lukbieli/DC_meter/case_model/DC_Meter_Case - Surface 7.stl

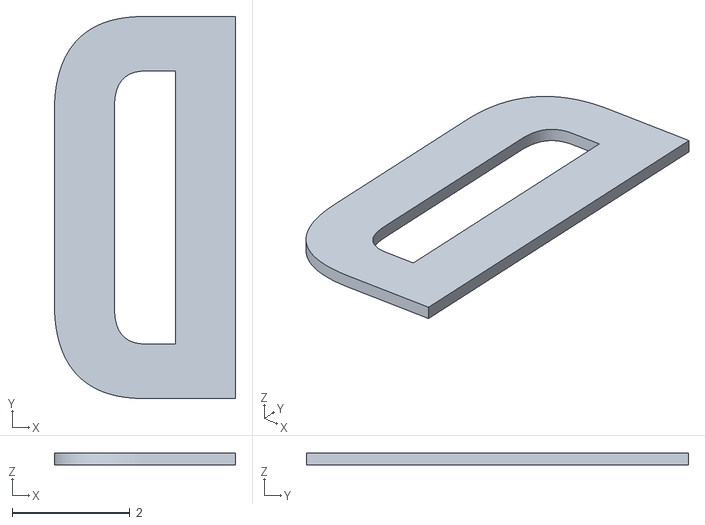
[picture p23: CAD file, 2025-07-14]
case_model/DC_Meter_Case - Surface 7.stl
3.08 x 6.49 x 0.2
