lukbieli/DC_meter/case_model/DC_Meter_Case - Surface 29.stl

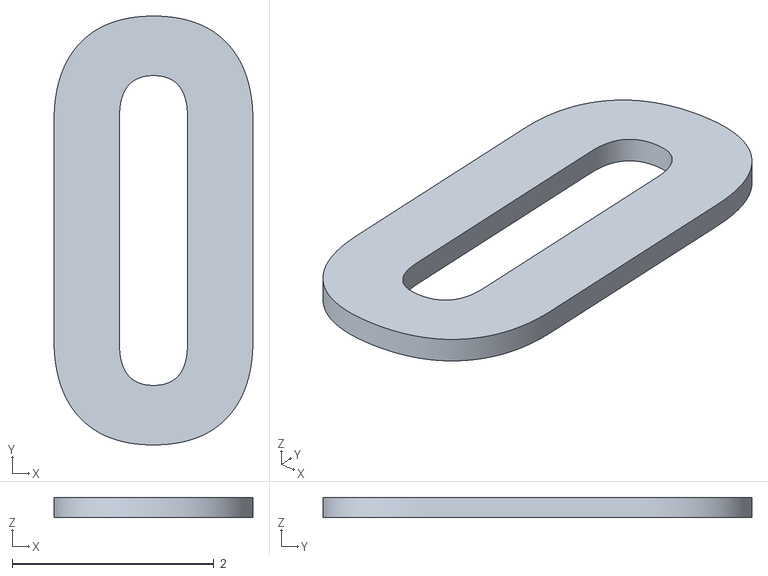
[picture p24: CAD file, 2025-07-14]
case_model/DC_Meter_Case - Surface 29.stl
1.97 x 4.26 x 0.2
