lukbieli/DC_meter/case_model/DC_Meter_Case - Surface 23.stl

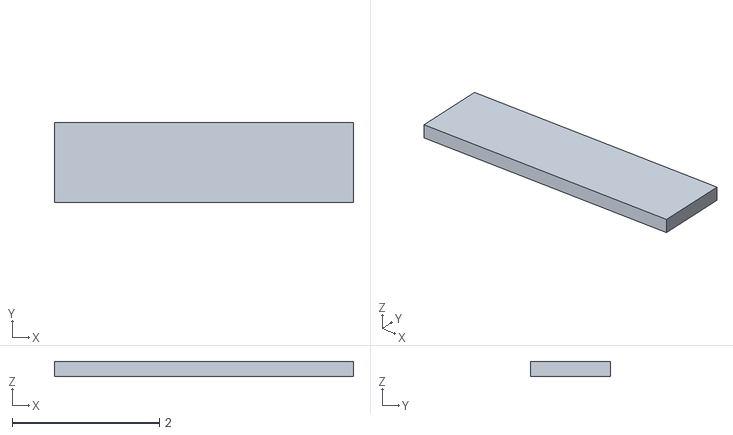
[picture p25: CAD file, 2025-07-14]
case_model/DC_Meter_Case - Surface 23.stl
4.06 x 1.08 x 0.2
