lukbieli/DC_meter/case_model/DC_Meter_Case - Surface 52.stl

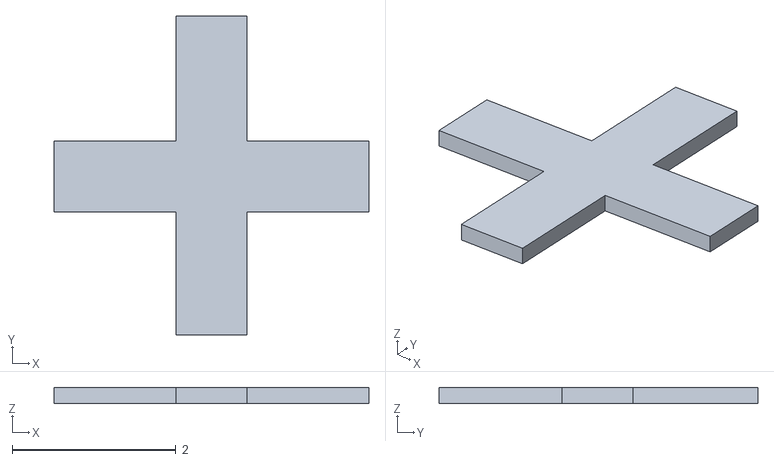
[picture p26: CAD file, 2025-07-14]
case_model/DC_Meter_Case - Surface 52.stl
3.84 x 3.89 x 0.2
