lukbieli/DC_meter/case_model/DC_Meter_Case - Surface 47.stl

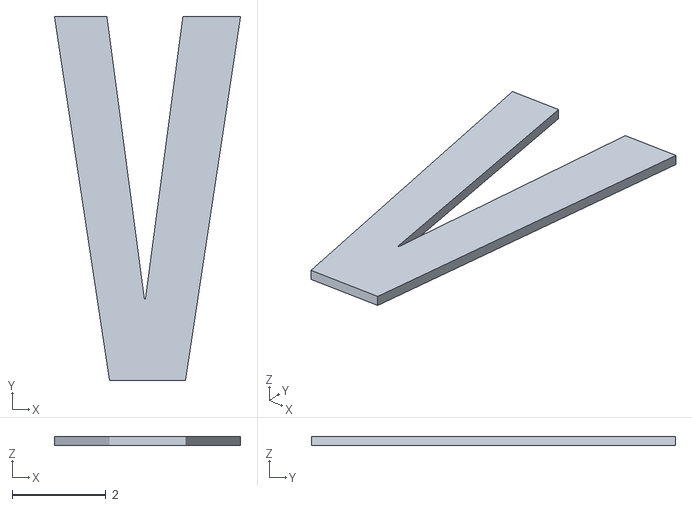
[picture p27: CAD file, 2025-07-14]
case_model/DC_Meter_Case - Surface 47.stl
3.98 x 7.78 x 0.2
