lukbieli/DC_meter/case_model/DC_Meter_Case - Surface 34.stl

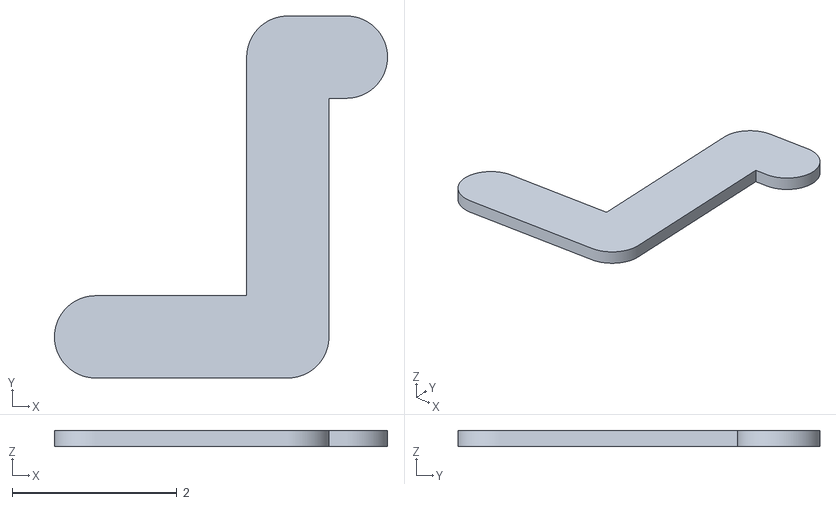
[picture p28: CAD file, 2025-07-14]
case_model/DC_Meter_Case - Surface 34.stl
4.05 x 4.40 x 0.2
