lukbieli/DC_meter/case_model/DC_Meter_Case - Surface 24.stl

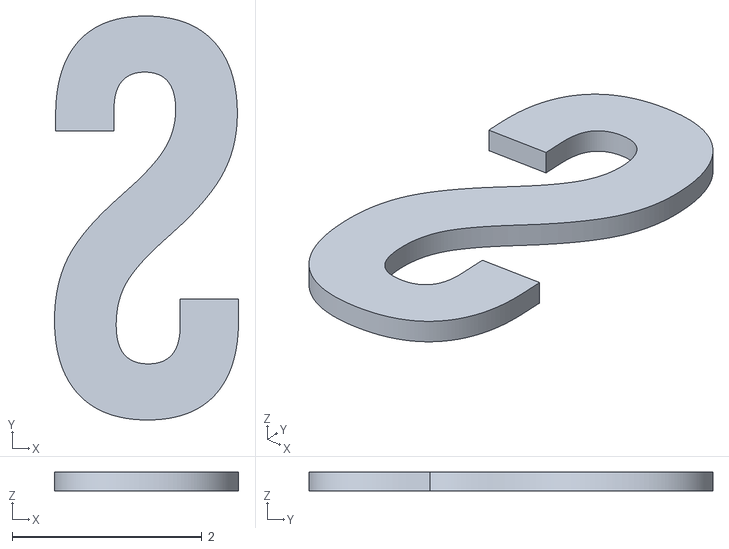
[picture p29: CAD file, 2025-07-14]
case_model/DC_Meter_Case - Surface 24.stl
1.94 x 4.26 x 0.2
