lukbieli/DC_meter/case_model/DC_Meter_Case - Surface 53.stl

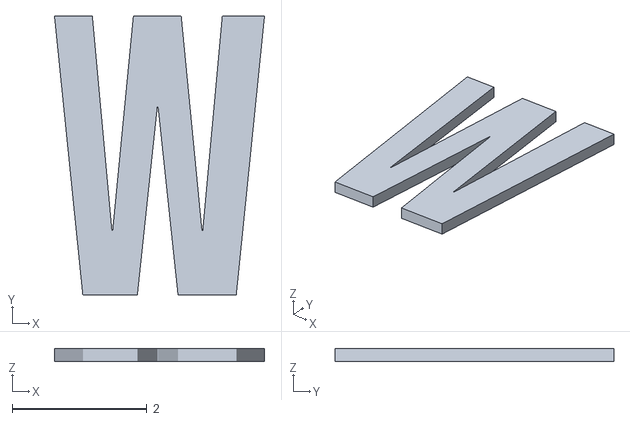
[picture p30: CAD file, 2025-07-14]
case_model/DC_Meter_Case - Surface 53.stl
3.11 x 4.14 x 0.2
