lukbieli/DC_meter/case_model/DC_Meter_Case - Surface 41.stl

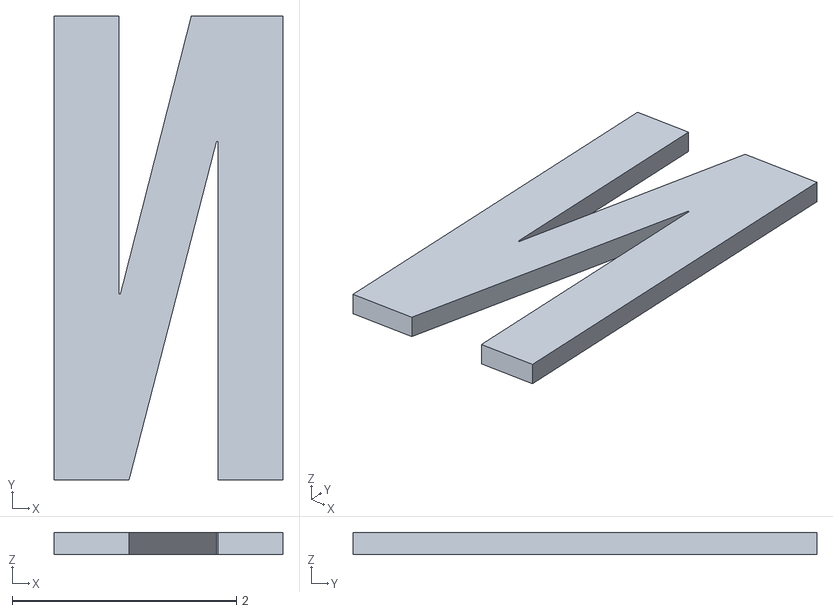
[picture p31: CAD file, 2025-07-14]
case_model/DC_Meter_Case - Surface 41.stl
2.04 x 4.14 x 0.2
