lukbieli/DC_meter/case_model/DC_Meter_Case - Surface 49.stl

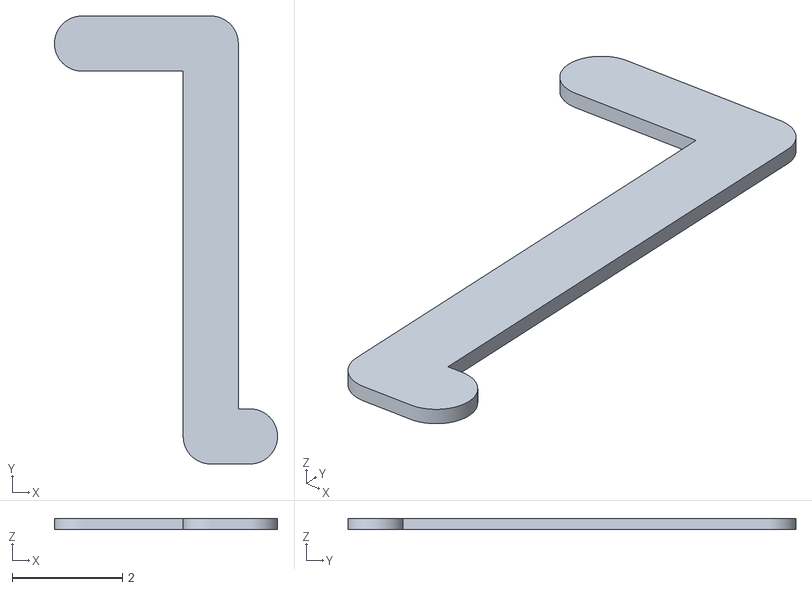
[picture p32: CAD file, 2025-07-14]
case_model/DC_Meter_Case - Surface 49.stl
4.05 x 8.13 x 0.2
