lukbieli/DC_meter/case_model/DC_Meter_Case - Surface 48.stl

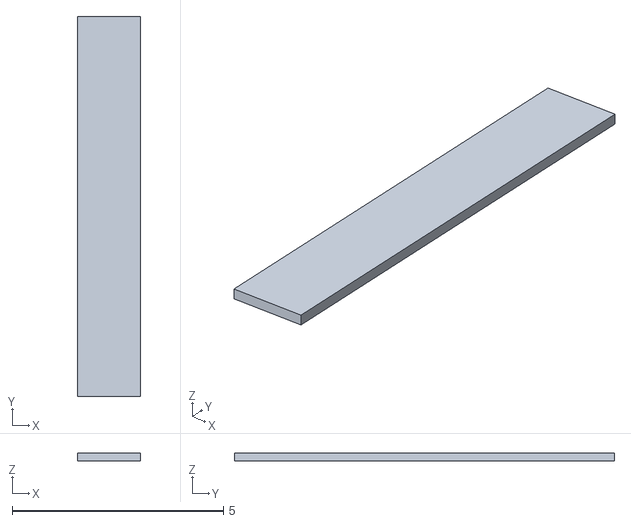
[picture p33: CAD file, 2025-07-14]
case_model/DC_Meter_Case - Surface 48.stl
1.50 x 9.00 x 0.2
