lukbieli/DC_meter/case_model/DC_Meter_Case - Surface 28.stl

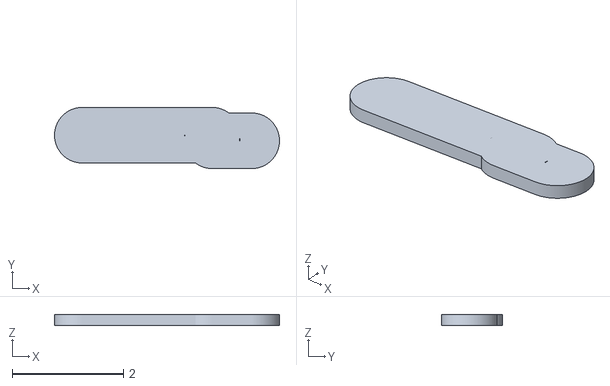
[picture p34: CAD file, 2025-07-14]
case_model/DC_Meter_Case - Surface 28.stl
4.05 x 1.10 x 0.2
