lukbieli/DC_meter/case_model/DC_Meter_Case - Surface 35.stl

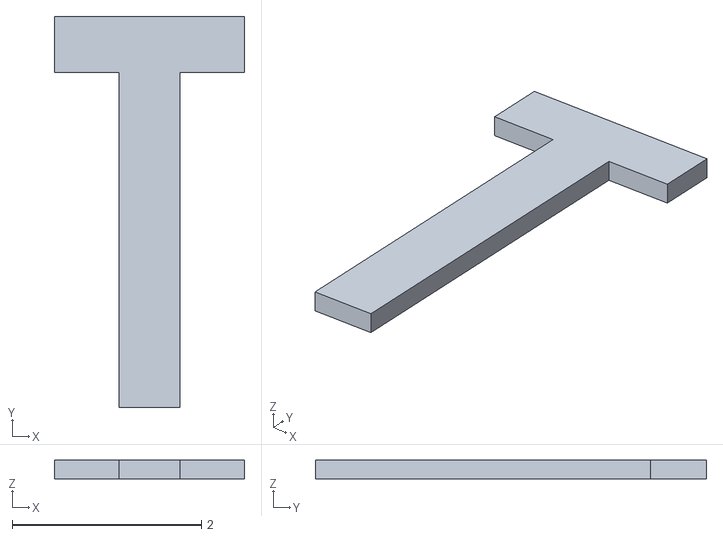
[picture p35: CAD file, 2025-07-14]
case_model/DC_Meter_Case - Surface 35.stl
2.01 x 4.14 x 0.2
