lukbieli/DC_meter/case_model/DC_Meter_Case - Surface 31.stl

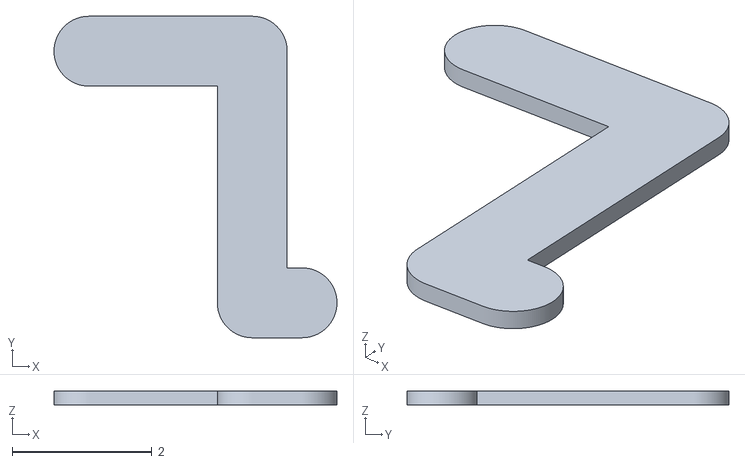
[picture p36: CAD file, 2025-07-14]
case_model/DC_Meter_Case - Surface 31.stl
4.05 x 4.60 x 0.2
