lukbieli/DC_meter/case_model/DC_Meter_Case - Surface 36.stl

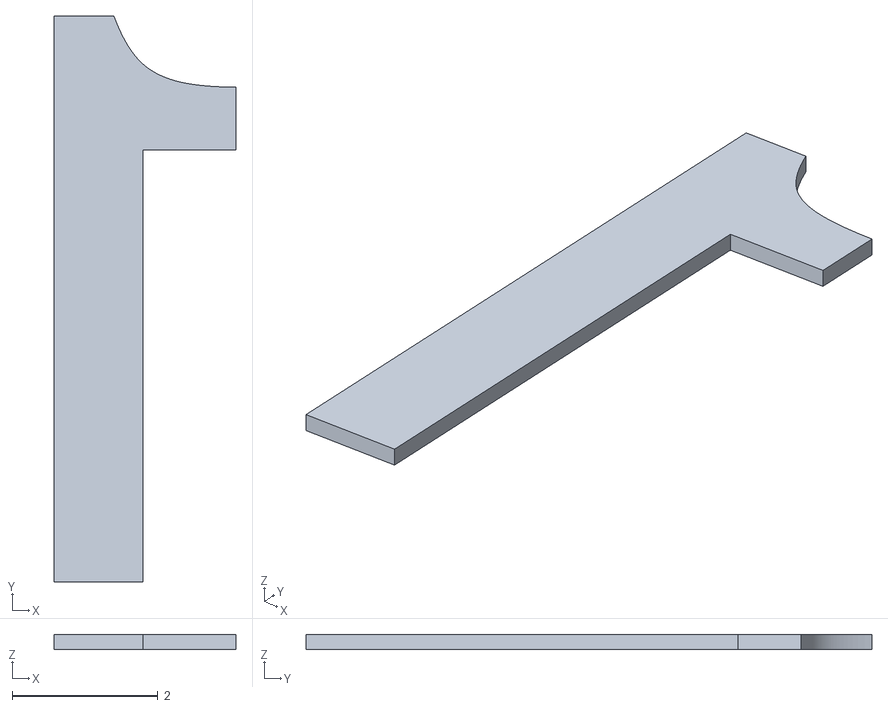
[picture p37: CAD file, 2025-07-14]
case_model/DC_Meter_Case - Surface 36.stl
2.50 x 7.78 x 0.2
