lukbieli/DC_meter/case_model/DC_Meter_Case - Surface 44.stl

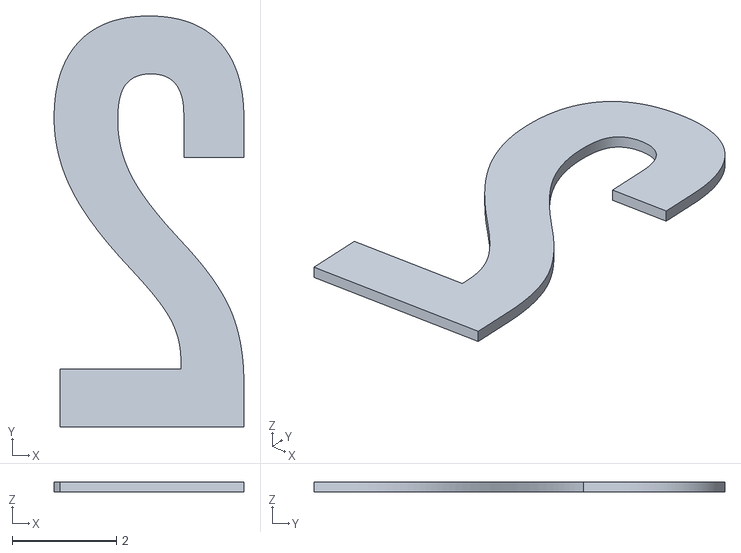
[picture p38: CAD file, 2025-07-14]
case_model/DC_Meter_Case - Surface 44.stl
3.64 x 7.89 x 0.2
