lukbieli/DC_meter/case_model/DC_Meter_Case - Surface 5.stl

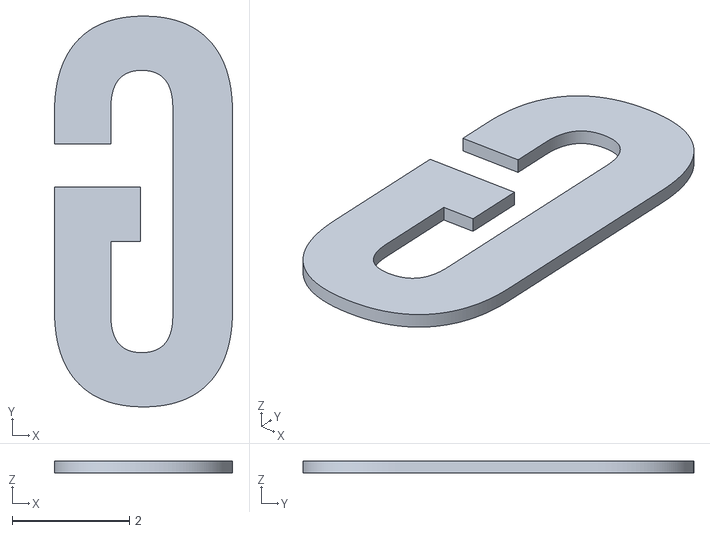
[picture p39: CAD file, 2025-07-14]
case_model/DC_Meter_Case - Surface 5.stl
3.04 x 6.67 x 0.2
