lukbieli/DC_meter/case_model/DC_Meter_Case - Surface 6.stl

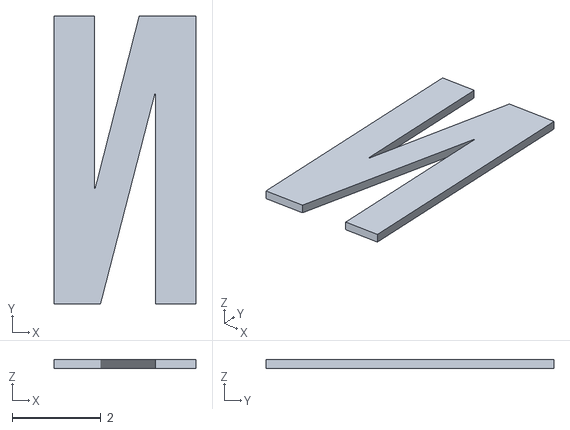
[picture p40: CAD file, 2025-07-14]
case_model/DC_Meter_Case - Surface 6.stl
3.20 x 6.49 x 0.2
