lukbieli/DC_meter/main/CurrentDrv.h

// SPDX-License-Identifier: MIT
// Copyright (c) 2025 Lukasz Bielinski

#ifndef CURRENTDRV_H
#define CURRENTDRV_H


#include <freertos/queue.h>
#include <esp_timer.h>
#include "ina219.h"

//pragma pack aligned to 1 byte struct with ina results
#pragma pack(1)
typedef struct {
    float voltage;      //!< Bus voltage, V
    float current;          //!< Current, A
    float power;            //!< Power, W
    float shunt_voltage;    //!< Shunt voltage, V
} ina219_data_raw_t;

typedef struct{
    ina219_data_raw_t ch1;
    ina219_data_raw_t ch2;
    ina219_data_raw_t ch3;
}ina219_full_data_t;
#pragma pack()

typedef struct CurrentDrv_ChannelCfg {
    bool voltage_enabled;  //!< Enable voltage measurement
    bool current_enabled;  //!< Enable current measurement
    bool power_enabled;    //!< Enable power measurement
    ina219_gain_t gain;  //!< Gain setting for current measurement
    ina219_bus_voltage_range_t bus_voltage_range;  //!< Bus voltage range setting
    ina219_resolution_t bus_voltage_resolution;  //!< Bus voltage resolution setting
    ina219_resolution_t shunt_voltage_resolution;  //!< Shunt voltage resolution setting
    uint8_t i2c_addr;  //!< I2C address of the INA219 device
} CurrentDrv_ChannelCfg_t;

typedef struct CurrentDrv_Cfg {
    CurrentDrv_ChannelCfg_t ch1;  //!< Channel 1 configuration
    CurrentDrv_ChannelCfg_t ch2;  //!< Channel 2 configuration
    CurrentDrv_ChannelCfg_t ch3;  //!< Channel 3 configuration
} CurrentDrv_Config_t;


/**
 * @brief Initialize the Current Driver module.
 */
void CurrentDrv_Init(void);

/**
 * @brief Main task for the Current Driver. Handles periodic measurement and queueing.
 * @param pvParameters FreeRTOS task parameter (unused).
 */
void CurrentDrv_Task(void *pvParameters);

/**
 * @brief Get the handle to the queue used for sending measurement data.
 * @return Pointer to the queue handle.
 */
QueueHandle_t* CurrentDrv_GetQueue(void);

/**
 * @brief Get the handle to the periodic timer used for measurements.
 * @return Pointer to the timer handle.
 */
esp_timer_handle_t* CurrentDrv_GetPeriodicTimer(void);

/**
 * @brief Set the configuration for all measurement channels.
 * @param config Pointer to the configuration structure.
 */
void CurrentDrv_SetChannelConfig(CurrentDrv_Config_t *config);

/**
 * @brief Get the current configuration for all measurement channels.
 * @param config Pointer to the configuration structure to fill.
 */
void CurrentDrv_GetChannelConfig(CurrentDrv_Config_t* config);

/**
 * @brief Set the period for the measurement timer.
 * @param period_us Timer period in microseconds.
 */
void CurrentDrv_SetTimerPeriod(uint32_t period_us);

/**
 * @brief Get the current timer period in microseconds.
 * @return Timer period in microseconds.
 */
uint32_t CurrentDrv_GetTimerPeriod(void);

/**
 * @brief Stop the periodic measurement timer.
 */
void CurrentDrv_StopTimer(void);

/**
 * @brief Start the periodic measurement timer.
 * @param auto_cfg_en Enable or disable auto-configuration of gain/range.
 */
void CurrentDrv_StartTimer(bool auto_cfg_en);

/**
 * @brief Get the averaged measurement data for all channels.
 * @param data Pointer to the structure to fill with averaged data.
 */
void CurrentDrv_GetAvgData(ina219_full_data_t *data);

#endif // CURRENTDRV_H
